OLIMEX/USB-gLINK/HARDWARE/USB-gLINK_Rev.C/USB-gLINK_Rev_C.pdf

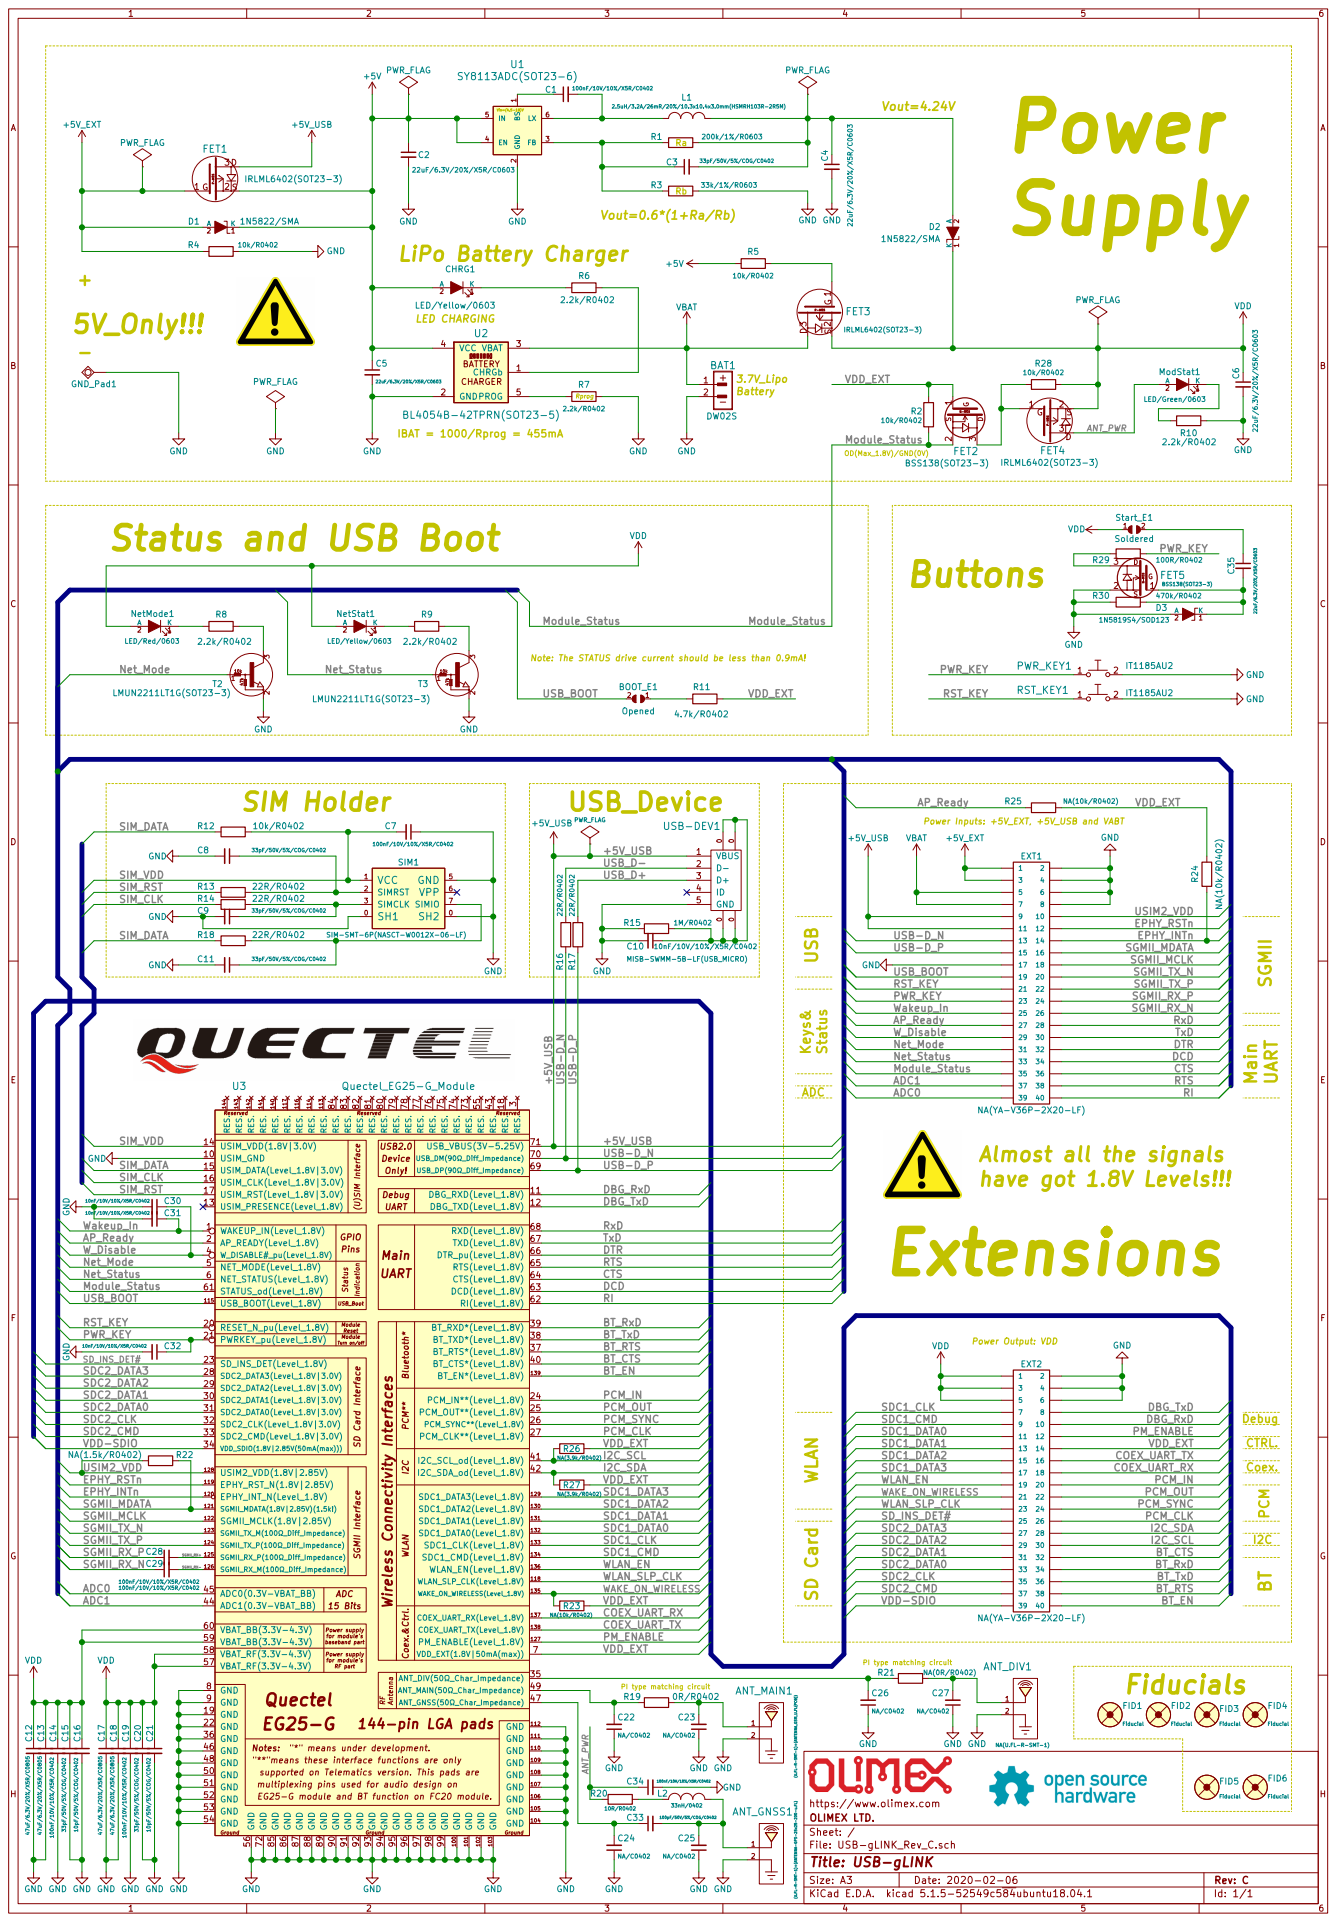
[picture p20: page 1]

AP_Ready Status and USB Boot

Power Inputs: +5V_EXT, +5V_USB and VABT

"*" means under development. "**"means these interface functions are only (U)SIM Interface

SIM-SMT-6P(NASCT-W0012X-06-LF)

ADC0 ADC1 PWR_KEY RST_KEY
Module Module multiplexing pins used for audio design on Notes:

Almost all the signals

for module's GPIO
RF part SD Card Interface SGMII Interface Status

SDC2_DATA1
2 ANT_MAIN1 (U.FL-R-SMT-1)+(ANTENNA_GSM_U.FL(PCB)) GND

Power supply Power supply Quectel

PI type matching circuit

supported on Telematics version. This pads are

EG25-G module and BT function on FC20 module.

File: USB-gLINK_Rev_C.sch Sheet: / OLIMEX LTD. https://www.olimex.com

Id: 1/1 Title: USB-gLINK
